Zebsterpasha/PicoMMU-bedslinger-compat/AutoShutdown/shell_command.cfg

[gcode_shell_command safe_shutdown]
command: python3 /home/pavel/printer_data/config/scripts/safe_shutdown.py
timeout: 7200
verbose: True

[gcode_macro AUTO_POWER_OFF]
gcode:
    {% if printer.print_stats.state == "printing" or printer.print_stats.state == "paused" %}
        { action_respond_info("🔄 Выключение запланировано после печати") }
        UPDATE_DELAYED_GCODE ID=auto_shutdown DURATION=1
    {% else %}
        { action_respond_info("⚡ Немедленное безопасное выключение") }
        RUN_SHELL_COMMAND CMD=safe_shutdown
    {% endif %}

[delayed_gcode auto_shutdown]
gcode:
    {% if printer.print_stats.state == "printing" or printer.print_stats.state == "paused" %}
        UPDATE_DELAYED_GCODE ID=auto_shutdown DURATION=60
    {% else %}
        { action_respond_info("❄️ Запускаю безопасное выключение") }
        RUN_SHELL_COMMAND CMD=safe_shutdown
    {% endif %}

[idle_timeout]
gcode:
    BASE_IDLE_TIMEOUT_GCODE

[gcode_macro BASE_IDLE_TIMEOUT_GCODE]
description: "Turn off hotend when idle timeout is reached"
gcode:
    SET_GCODE_VARIABLE MACRO=_SP_VARS VARIABLE=resume_ext VALUE={printer.extruder.target}
    SET_GCODE_VARIABLE MACRO=_SP_VARS VARIABLE=resume_bed VALUE={printer.heater_bed.target}

    RESPOND MSG="Idle timeout: turning off hotend"
    M104 S0  ; turn off extruder heater
